ZeroGDesign/Nebula/DFXs/255_DXF_Panels/Nebula_255_Top_Panel.dxf

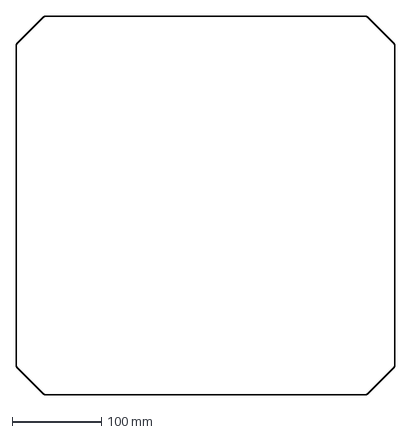
[picture p53: CAD file, 2025-05-16]
DFXs/255_DXF_Panels/Nebula_255_Top_Panel.dxf
424.0 x 424.0 mm
