ZeroGDesign/Nebula/DFXs/370_DXF_Panels/Optional-Nebula_370_ACM_Side_Panel_x2.dxf

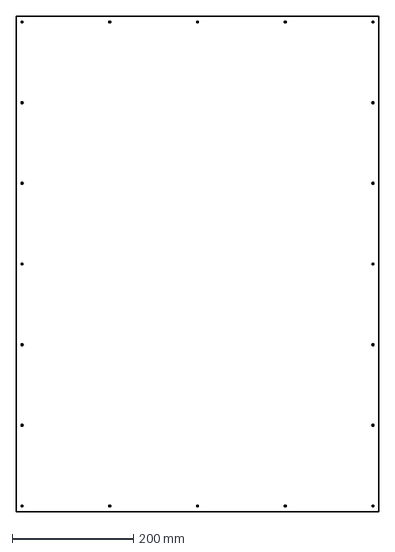
[picture p54: CAD file, 2025-07-06]
DFXs/370_DXF_Panels/Optional-Nebula_370_ACM_Side_Panel_x2.dxf
599.5 x 819.5 mm
