ZeroGDesign/Nebula/STLs/Doors/5_5mm_Thick_Front_ Doors/Base_Hinge_5-5mm.stl

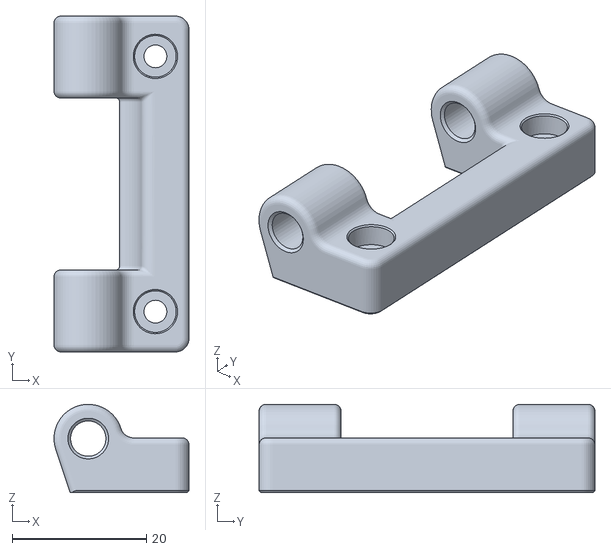
[picture p55: CAD file, 2025-05-16]
STLs/Doors/5_5mm_Thick_Front_ Doors/Base_Hinge_5-5mm.stl
20.1 x 50.0 x 13.1
