ZeroGDesign/Nebula/STLs/Doors/Nebula_370/Right_Logo_Hinge_X2.stl

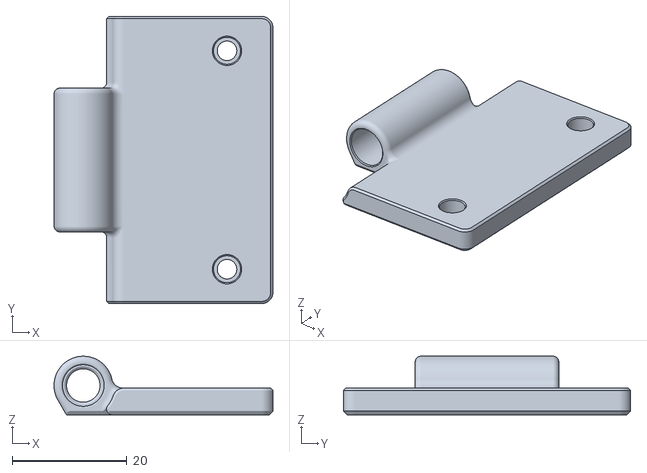
[picture p56: CAD file, 2025-05-16]
STLs/Doors/Nebula_370/Right_Logo_Hinge_X2.stl
38.1 x 50.0 x 10.2
