ZeroGDesign/Nebula/STLs/Electronics_Cover/Nebula_255/Filler_Panel_Right_Back.stl

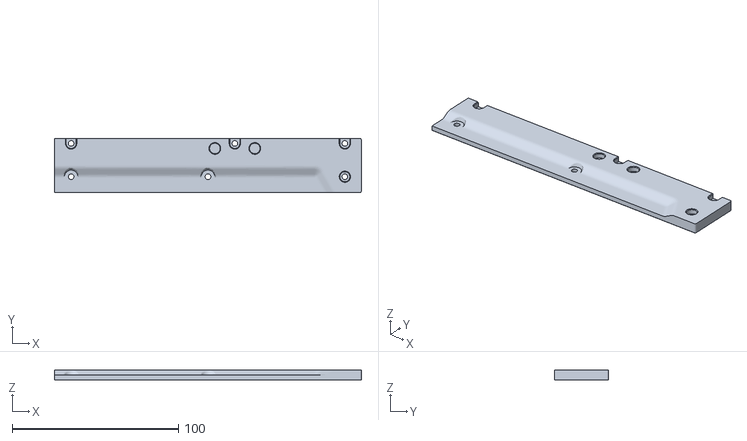
[picture p57: CAD file, 2025-05-16]
STLs/Electronics_Cover/Nebula_255/Filler_Panel_Right_Back.stl
184.5 x 32.5 x 6.00
