ZeroGDesign/Nebula/STLs/Electronics_Cover/Nebula_370/Back_Filler_Left.stl

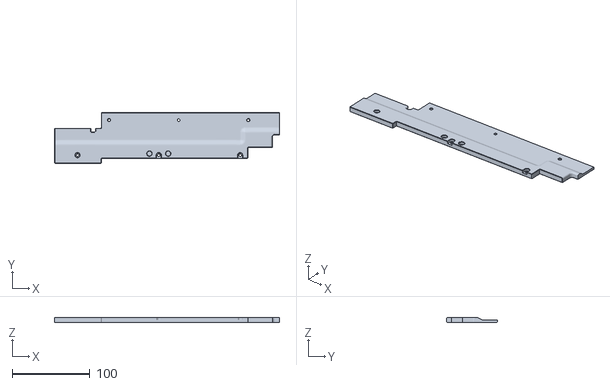
[picture p58: CAD file, 2025-05-16]
STLs/Electronics_Cover/Nebula_370/Back_Filler_Left.stl
288.5 x 65.0 x 6.00
