ZeroGDesign/Nebula/STLs/Skirts/Nebula_255/SK_Center_Logo-v0-0-5.3mf

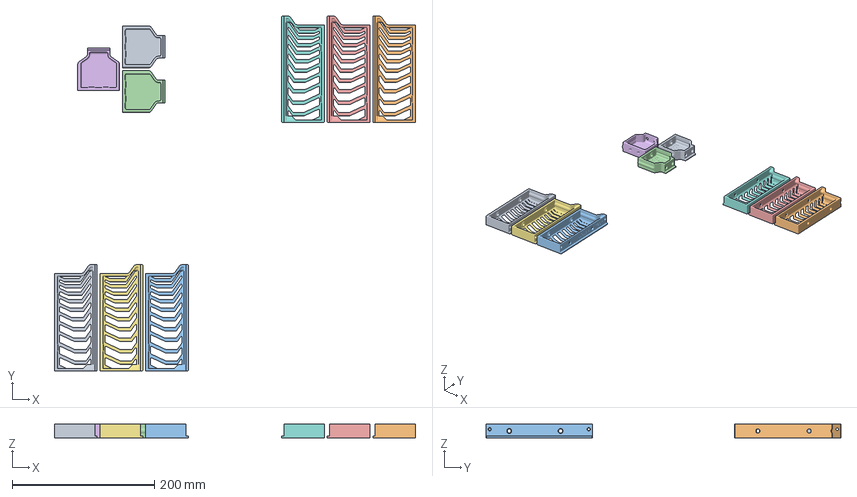
[picture p60: CAD file, 2025-07-06]
STLs/Skirts/Nebula_255/SK_Center_Logo-v0-0-5.3mf
507.2 x 498.3 x 20.0 mm
SK_Center_Logo-v0-0-5.stl_1 x 3
SK_330_L_V0-0-4.stl x 3
SK_330_R_V0-0-4.stl x 3
