ZeroGDesign/Nebula/STLs/Skirts/Nebula_370/Short Skirt/SK_Center_Logo-v0-0-5.stl

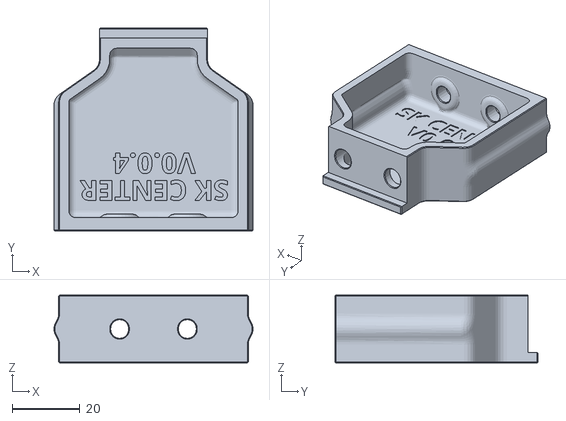
[picture p61: CAD file, 2025-05-16]
STLs/Skirts/Nebula_370/Short Skirt/SK_Center_Logo-v0-0-5.stl
58.8 x 60.0 x 20.0
