ZeroGDesign/Nebula/DFXs/255_DXF_Panels/Nebula_255_Bottom_Panel.dxf

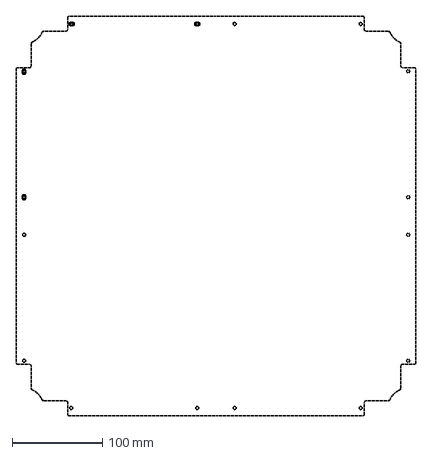
[picture p62: CAD file, 2025-05-16]
DFXs/255_DXF_Panels/Nebula_255_Bottom_Panel.dxf
442.5 x 442.5 mm
