ZeroGDesign/Nebula/DFXs/370_DXF_Panels/Nebula_370_Split_Door_x2.dxf

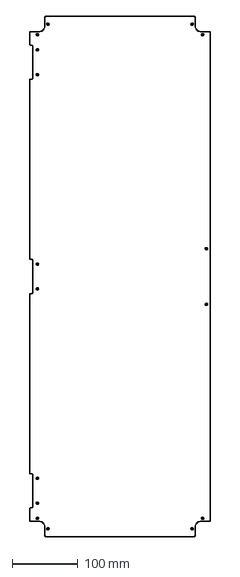
[picture p63: CAD file, 2025-05-16]
DFXs/370_DXF_Panels/Nebula_370_Split_Door_x2.dxf
275.9 x 794.0 mm
