ZeroGDesign/Nebula/STLs/Doors/5_5mm_Thick_Front_ Doors/Door_Handle_Spacer_5-5mm.stl

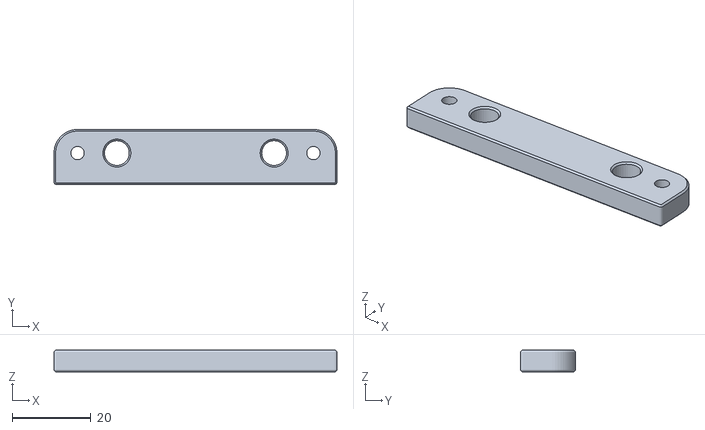
[picture p64: CAD file, 2025-05-16]
STLs/Doors/5_5mm_Thick_Front_ Doors/Door_Handle_Spacer_5-5mm.stl
72.0 x 14.0 x 5.50
