ZeroGDesign/Nebula/STLs/Doors/Magnet_Inside_Frame_Mount_x2.stl

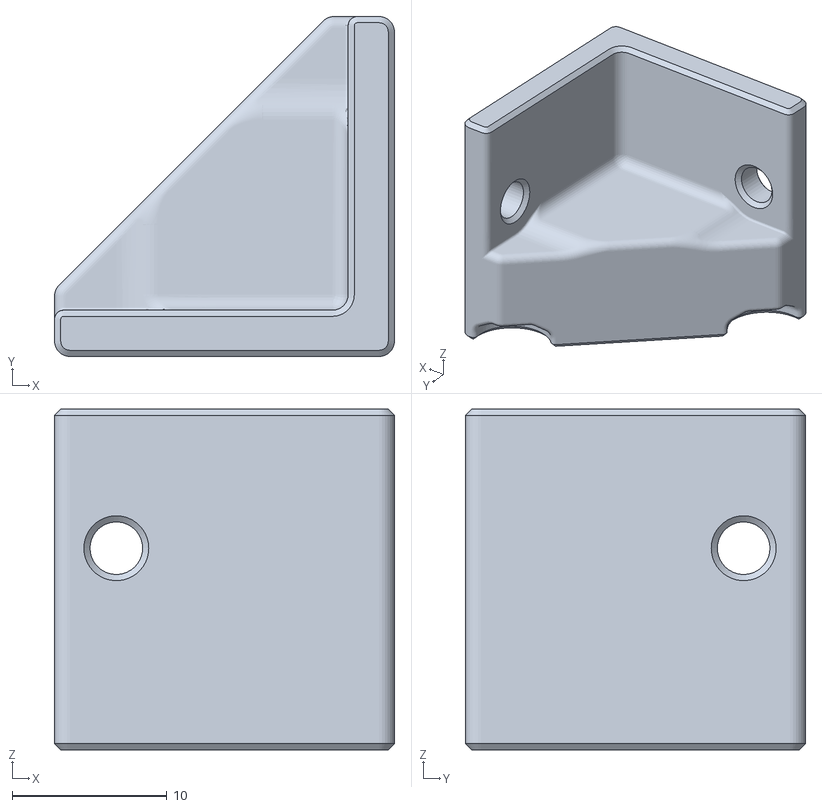
[picture p65: CAD file, 2025-05-16]
STLs/Doors/Magnet_Inside_Frame_Mount_x2.stl
22.0 x 22.0 x 22.0
