ZeroGDesign/Nebula/STLs/Doors/Nebula_370/a_Right_Handle.stl

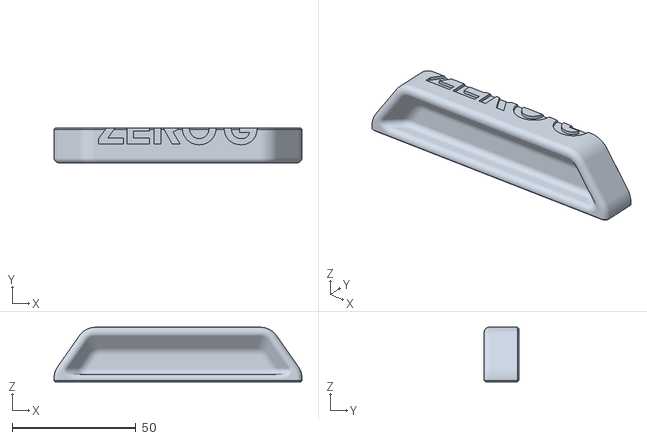
[picture p66: CAD file, 2025-05-16]
STLs/Doors/Nebula_370/a_Right_Handle.stl
100.0 x 14.0 x 22.0
