ZeroGDesign/Nebula/STLs/Electronics_Cover/Nebula_255/Back_Filler_Right.stl

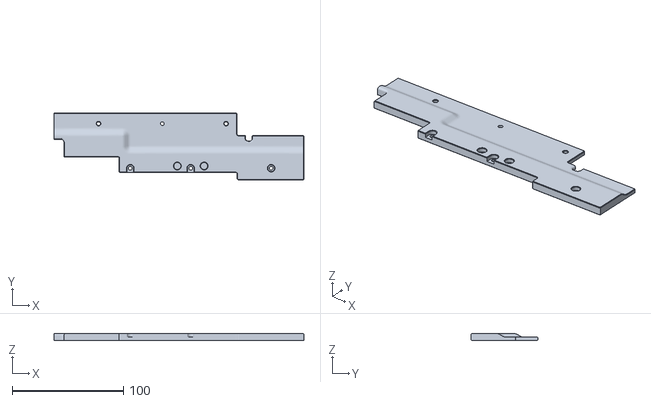
[picture p67: CAD file, 2025-05-16]
STLs/Electronics_Cover/Nebula_255/Back_Filler_Right.stl
224.5 x 60.0 x 6.00
