ZeroGDesign/Nebula/STLs/Misc/Nebula_Right_Stepper_Bottom.stl

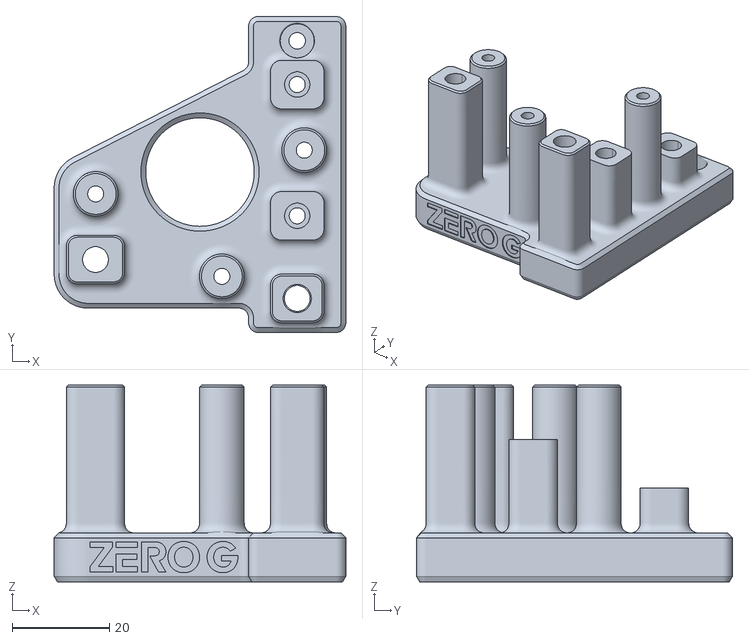
[picture p69: CAD file, 2025-05-16]
STLs/Misc/Nebula_Right_Stepper_Bottom.stl
60.0 x 65.0 x 40.5
