ZeroGDesign/Nebula/STLs/Optional_5mm_slot_with_files/Front_Tower_Right_-_5mm.stl

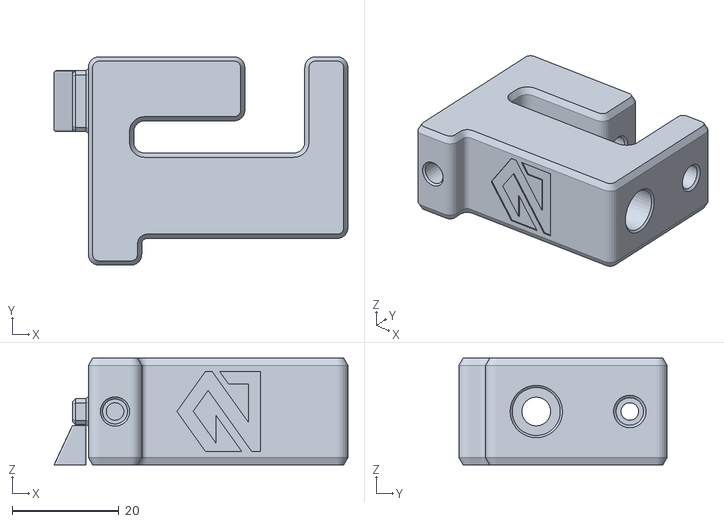
[picture p70: CAD file, 2025-05-16]
STLs/Optional_5mm_slot_with_files/Front_Tower_Right_-_5mm.stl
55.0 x 39.0 x 20.0
