ZeroGDesign/Nebula/STLs/Panels/Panel_Clip_Hollow.stl

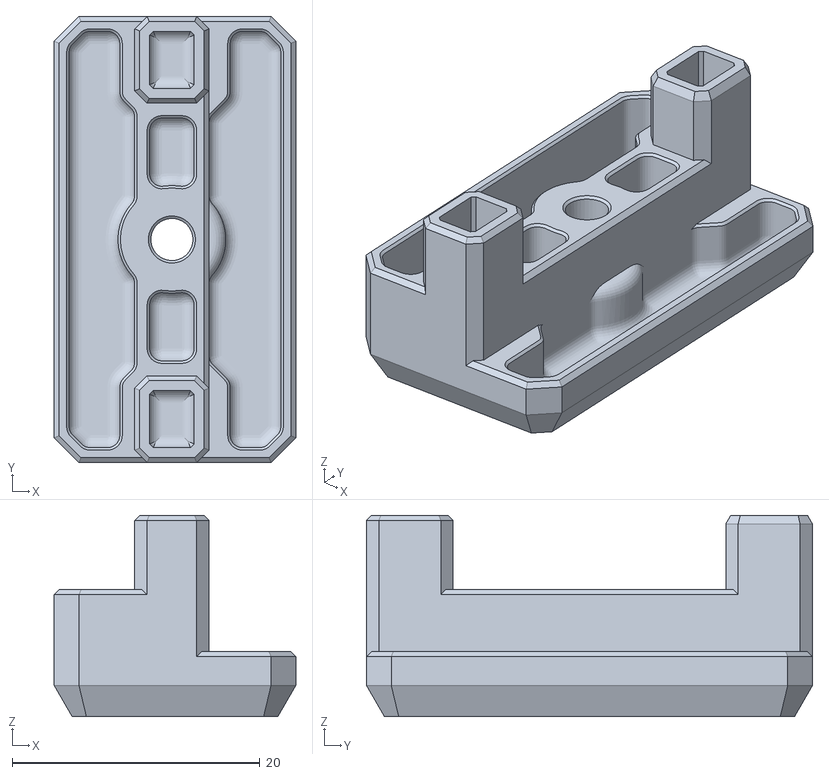
[picture p71: CAD file, 2025-05-16]
STLs/Panels/Panel_Clip_Hollow.stl
19.5 x 36.0 x 16.2
