ZeroGDesign/Nebula/STLs/Skirts/Nebula_370/Full Skirt/SK-458-R_x2.stl

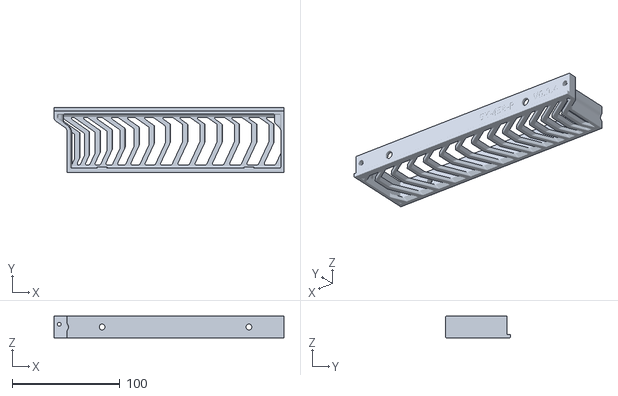
[picture p72: CAD file, 2025-05-16]
STLs/Skirts/Nebula_370/Full Skirt/SK-458-R_x2.stl
213.1 x 60.0 x 20.0
