ZeroGDesign/Nebula/DFXs/255_DXF_Panels/Nebula_255_Side_Panel_x3.dxf

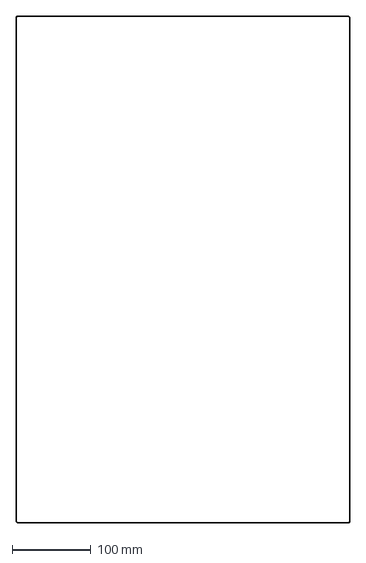
[picture p73: CAD file, 2025-05-16]
DFXs/255_DXF_Panels/Nebula_255_Side_Panel_x3.dxf
424.0 x 644.0 mm
