ZeroGDesign/Nebula/DFXs/370_DXF_Panels/Nebula_370_Back_Panel.dxf

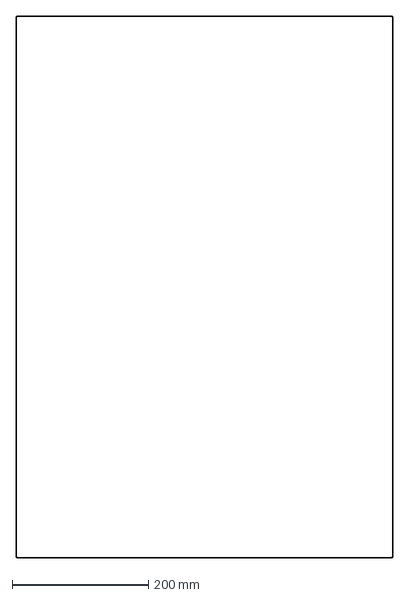
[picture p74: CAD file, 2025-05-16]
DFXs/370_DXF_Panels/Nebula_370_Back_Panel.dxf
552.0 x 794.0 mm
