ZeroGDesign/Nebula/STLs/Doors/Nebula_255/Base_Hinge_X3.stl

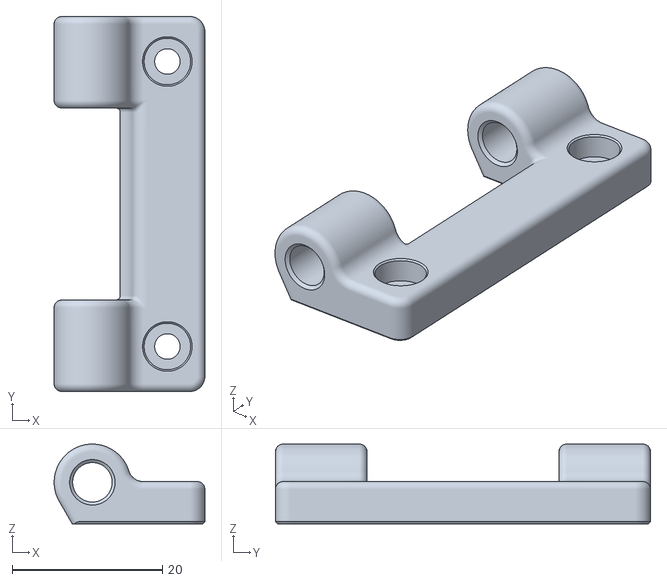
[picture p75: CAD file, 2025-05-16]
STLs/Doors/Nebula_255/Base_Hinge_X3.stl
20.1 x 50.0 x 10.6
