ZeroGDesign/Nebula/STLs/Electronics_Cover/Nebula_255/Clip_Top_x8.stl

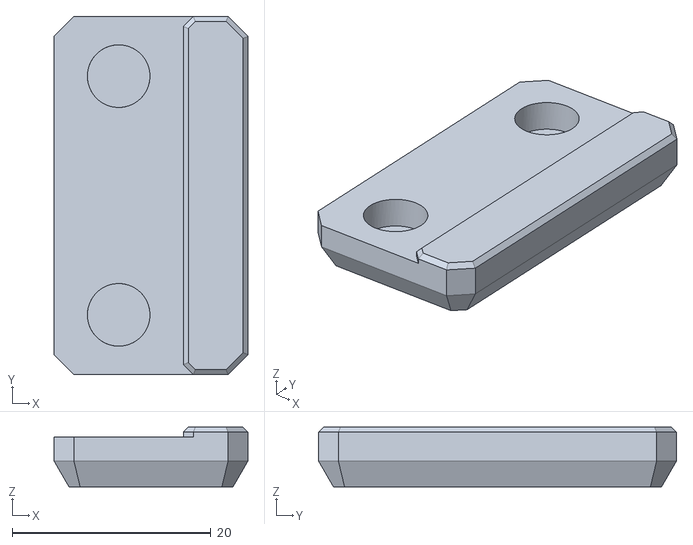
[picture p76: CAD file, 2025-05-16]
STLs/Electronics_Cover/Nebula_255/Clip_Top_x8.stl
19.5 x 36.0 x 6.00
