ZeroGDesign/Nebula/STLs/Misc/Beta_Spool_Holder_M1_Enclosed.stl

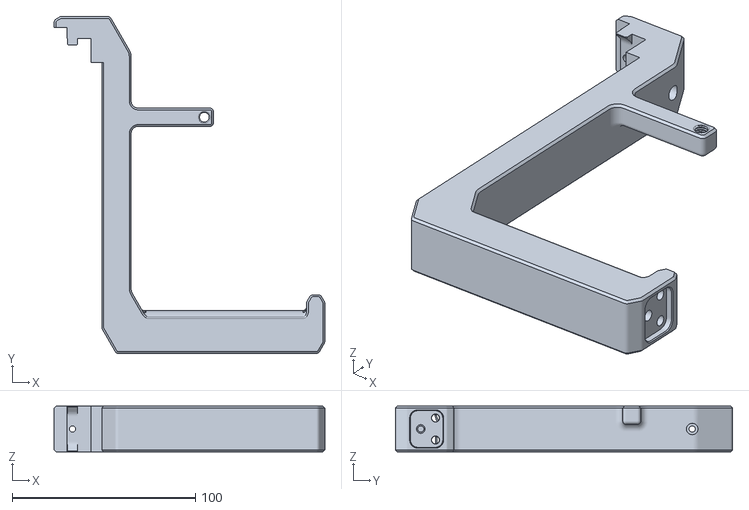
[picture p77: CAD file, 2025-05-16]
STLs/Misc/Beta_Spool_Holder_M1_Enclosed.stl
147.8 x 184.0 x 25.0
