ZeroGDesign/Nebula/STLs/Skirts/Nebula_370/Short Skirt/SK-435-L_V0-0-4.stl

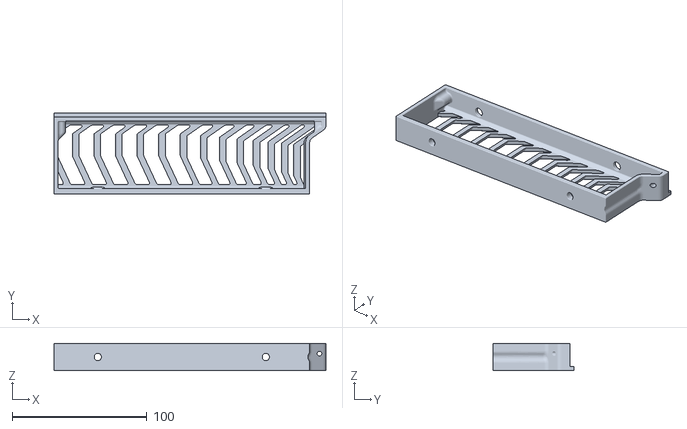
[picture p79: CAD file, 2025-05-16]
STLs/Skirts/Nebula_370/Short Skirt/SK-435-L_V0-0-4.stl
201.6 x 60.0 x 20.0
