ZeroGDesign/Nebula/DFXs/255_DXF_Panels/Nebula_255_Front_Door.dxf

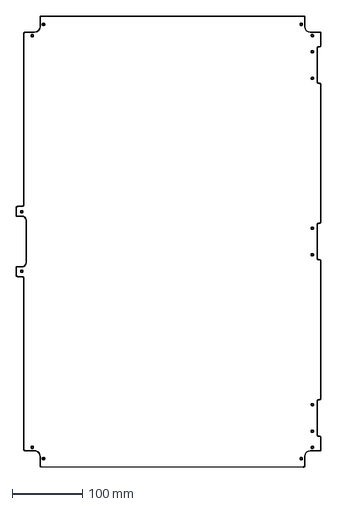
[picture p80: CAD file, 2025-05-16]
DFXs/255_DXF_Panels/Nebula_255_Front_Door.dxf
435.0 x 644.0 mm
