ZeroGDesign/Nebula/DFXs/370_DXF_Panels/Nebula_370_Bottom_Extension.dxf

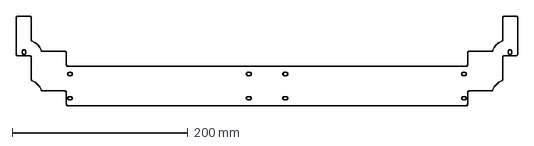
[picture p81: CAD file, 2025-05-16]
DFXs/370_DXF_Panels/Nebula_370_Bottom_Extension.dxf
570.5 x 102.0 mm
