ZeroGDesign/Nebula/STLs/Doors/Nebula_255/Middle_Hinge.stl

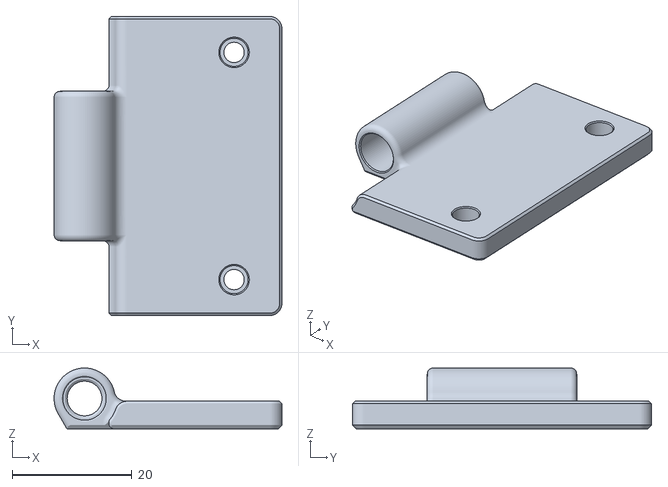
[picture p82: CAD file, 2025-05-16]
STLs/Doors/Nebula_255/Middle_Hinge.stl
38.1 x 50.0 x 10.2
