ZeroGDesign/Nebula/STLs/Doors/Nebula_370/Center_Magnet_Latch.stl

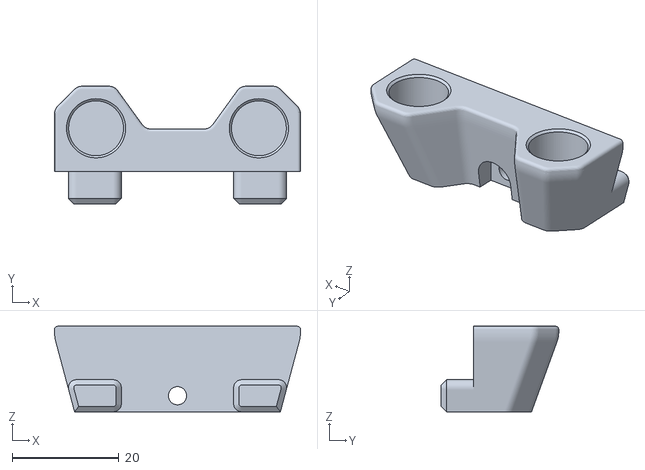
[picture p83: CAD file, 2025-05-16]
STLs/Doors/Nebula_370/Center_Magnet_Latch.stl
46.0 x 22.0 x 16.0
