ZeroGDesign/Nebula/STLs/Electronics_Cover/Nebula_255/Back_Filler_Left.stl

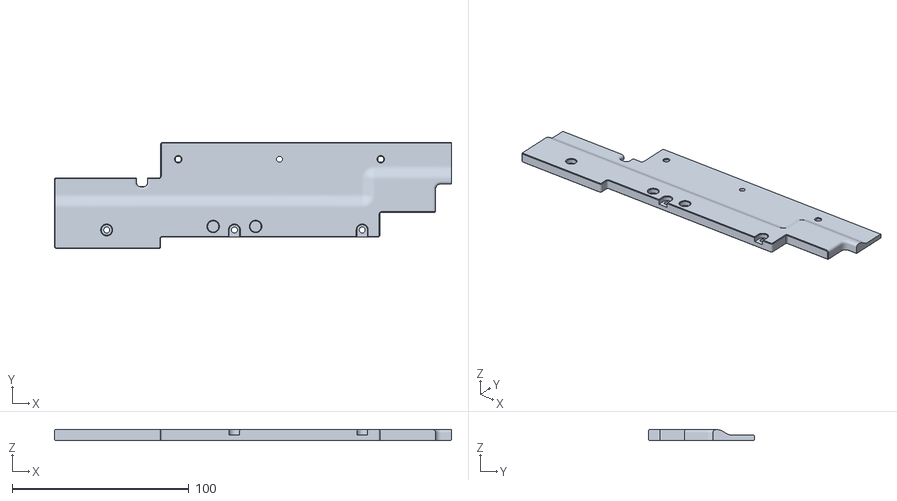
[picture p84: CAD file, 2025-05-16]
STLs/Electronics_Cover/Nebula_255/Back_Filler_Left.stl
224.5 x 60.0 x 6.00
