ZeroGDesign/Nebula/DFXs/255_DXF_Panels/Nebula_255_Deck_Panel.dxf

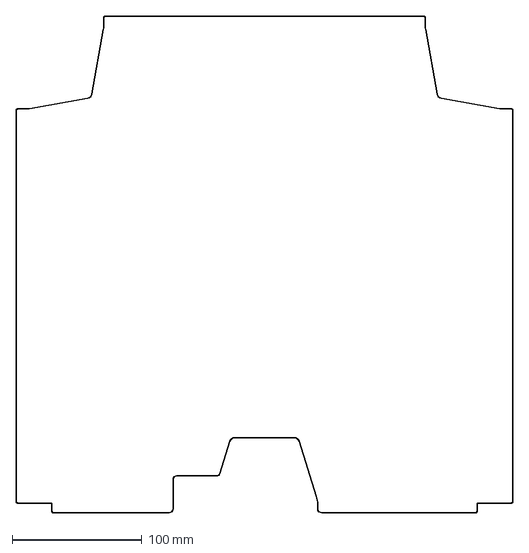
[picture p86: CAD file, 2025-05-16]
DFXs/255_DXF_Panels/Nebula_255_Deck_Panel.dxf
383.0 x 383.0 mm
