ZeroGDesign/Nebula/DFXs/370_DXF_Panels/Nebula_370_Bottom_Panel.dxf

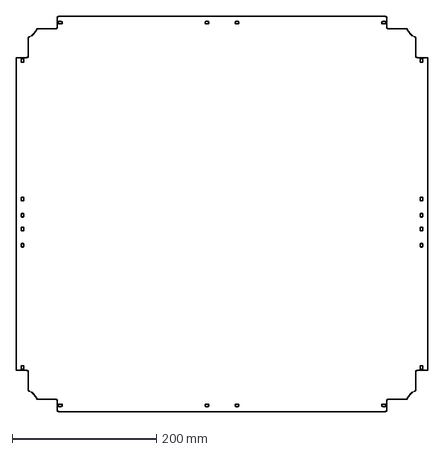
[picture p87: CAD file, 2025-05-16]
DFXs/370_DXF_Panels/Nebula_370_Bottom_Panel.dxf
570.5 x 547.5 mm
