ZeroGDesign/Nebula/STLs/Doors/Nebula_255/Door_Handle.stl

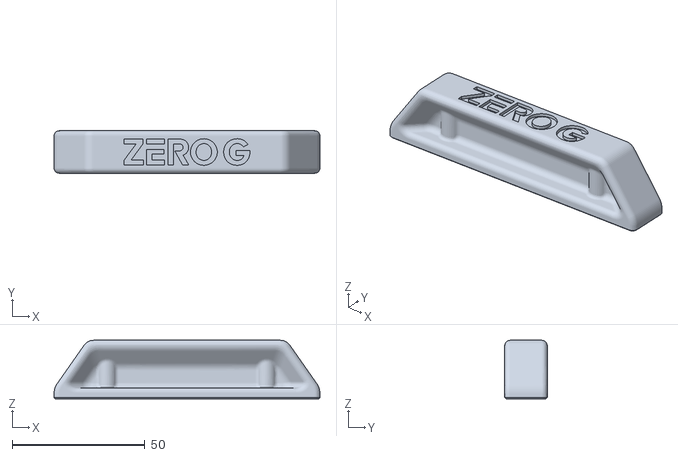
[picture p88: CAD file, 2025-05-16]
STLs/Doors/Nebula_255/Door_Handle.stl
100.0 x 16.0 x 22.0
