ZeroGDesign/Nebula/STLs/Electronics_Cover/Nebula_255/Filler_Panel_Left_Back.stl

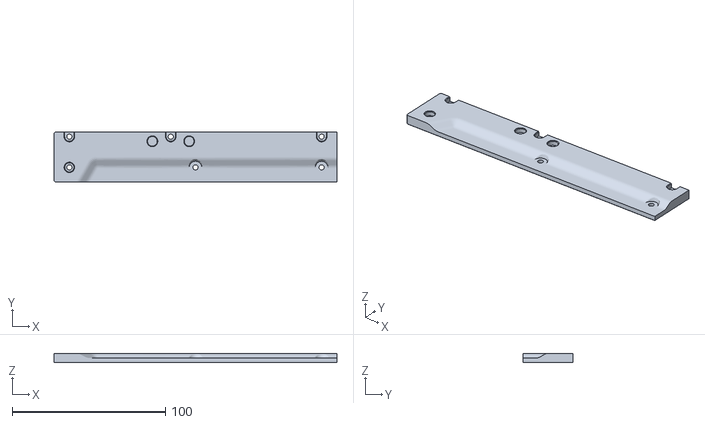
[picture p89: CAD file, 2025-05-16]
STLs/Electronics_Cover/Nebula_255/Filler_Panel_Left_Back.stl
184.5 x 32.5 x 6.00
