ZeroGDesign/Nebula/STLs/Skirts/Nebula_255/SK_330_L_V0-0-4_IEC.stl

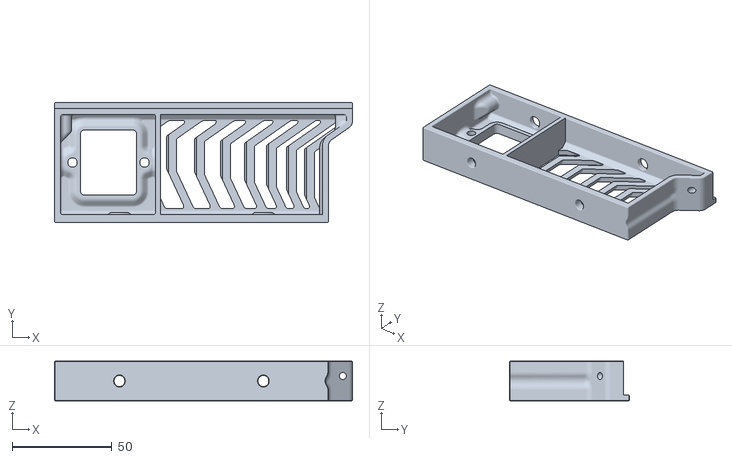
[picture p90: CAD file, 2025-07-06]
STLs/Skirts/Nebula_255/SK_330_L_V0-0-4_IEC.stl
149.1 x 60.0 x 20.0
