ZeroGDesign/Nebula/STLs/Skirts/Nebula_370/Full Skirt/Nebula_370_Extension_Brace_x2.stl

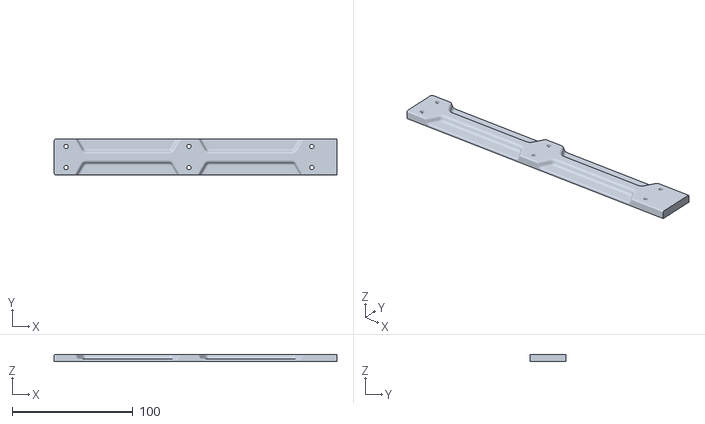
[picture p91: CAD file, 2025-05-16]
STLs/Skirts/Nebula_370/Full Skirt/Nebula_370_Extension_Brace_x2.stl
234.1 x 30.0 x 6.00
