ZeroGDesign/Nebula/STLs/Skirts/Nebula_370/Short Skirt/5_Plus_E_Rear_Skirt_Wing_L.stl

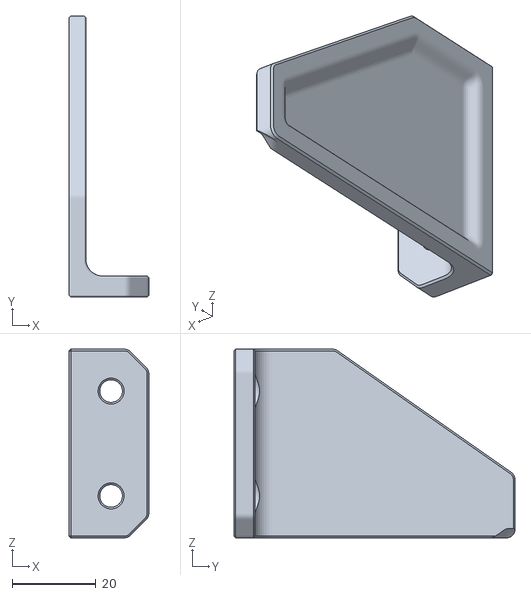
[picture p92: CAD file, 2025-05-16]
STLs/Skirts/Nebula_370/Short Skirt/5_Plus_E_Rear_Skirt_Wing_L.stl
19.0 x 67.0 x 45.0
