ZeroGDesign/Nebula/DFXs/370_DXF_Panels/Nebula_370_Top_Panel.dxf

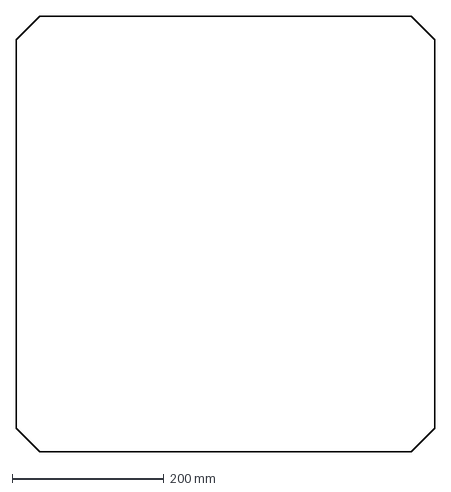
[picture p93: CAD file, 2025-05-16]
DFXs/370_DXF_Panels/Nebula_370_Top_Panel.dxf
552.0 x 574.0 mm
