ZeroGDesign/Nebula/STLs/Doors/Nebula_255/Door_Handle_Spacer_3mm.stl

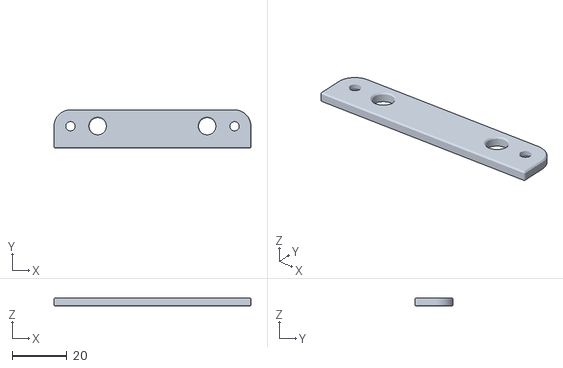
[picture p94: CAD file, 2025-05-16]
STLs/Doors/Nebula_255/Door_Handle_Spacer_3mm.stl
72.0 x 14.0 x 3.00
