ZeroGDesign/Nebula/STLs/Electronics_Cover/Nebula_255/Filler_Panel_Right_Front.stl

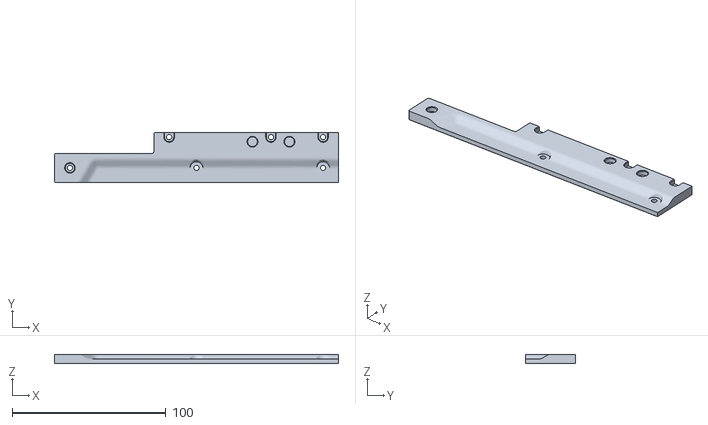
[picture p95: CAD file, 2025-05-16]
STLs/Electronics_Cover/Nebula_255/Filler_Panel_Right_Front.stl
184.5 x 32.5 x 6.00
