ZeroGDesign/Nebula/STLs/Electronics_Cover/Nebula_370/Filler_Panel_Right_Back.stl

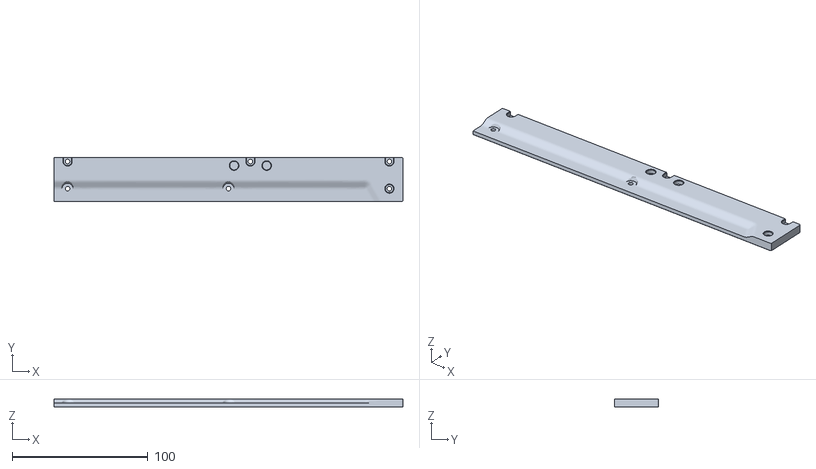
[picture p96: CAD file, 2025-05-16]
STLs/Electronics_Cover/Nebula_370/Filler_Panel_Right_Back.stl
257.0 x 32.5 x 6.00
