ZeroGDesign/Nebula/DFXs/370_DXF_Panels/Nebula_370_Side_Panel_x2.dxf

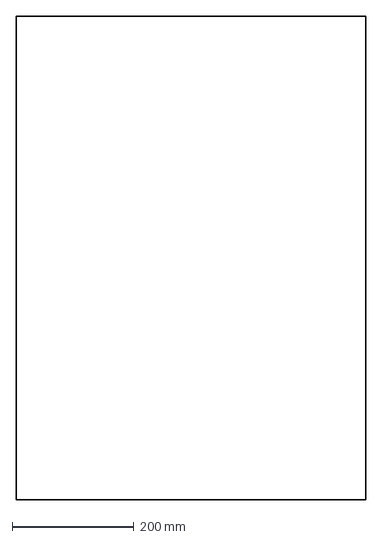
[picture p98: CAD file, 2025-05-16]
DFXs/370_DXF_Panels/Nebula_370_Side_Panel_x2.dxf
574.0 x 794.0 mm
