ZeroGDesign/Nebula/STLs/Doors/Nebula_255/Door_Magnet_Latch.stl

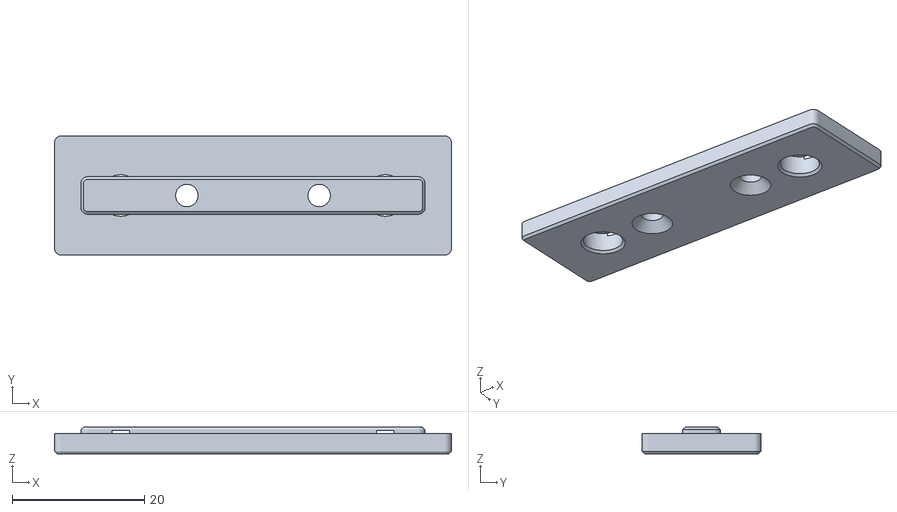
[picture p99: CAD file, 2025-05-16]
STLs/Doors/Nebula_255/Door_Magnet_Latch.stl
60.0 x 18.0 x 4.05
