ZeroGDesign/Nebula/DFXs/370_DXF_Panels/Nebula_370_Deck_Panel.dxf

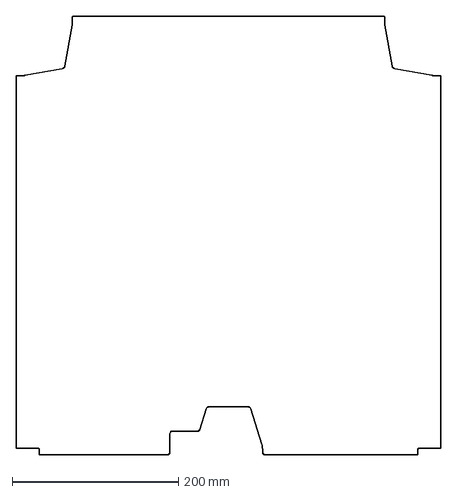
[picture p100: CAD file, 2025-05-16]
DFXs/370_DXF_Panels/Nebula_370_Deck_Panel.dxf
511.0 x 528.0 mm
