ZeroGDesign/Nebula/STLs/Skirts/Nebula_370/Full Skirt/SK-458-L_SW-IEC_x1.stl

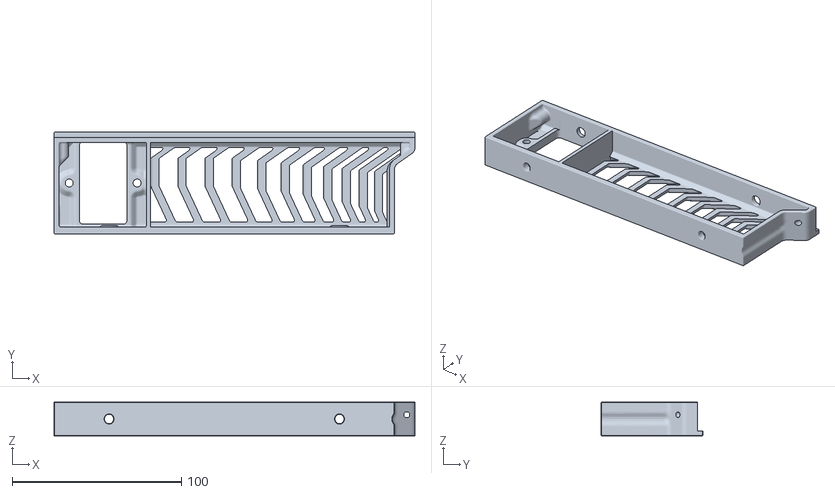
[picture p101: CAD file, 2025-05-16]
STLs/Skirts/Nebula_370/Full Skirt/SK-458-L_SW-IEC_x1.stl
213.1 x 60.0 x 20.0
